DarcyJProjects/stm32-plc-project/Media/2.png

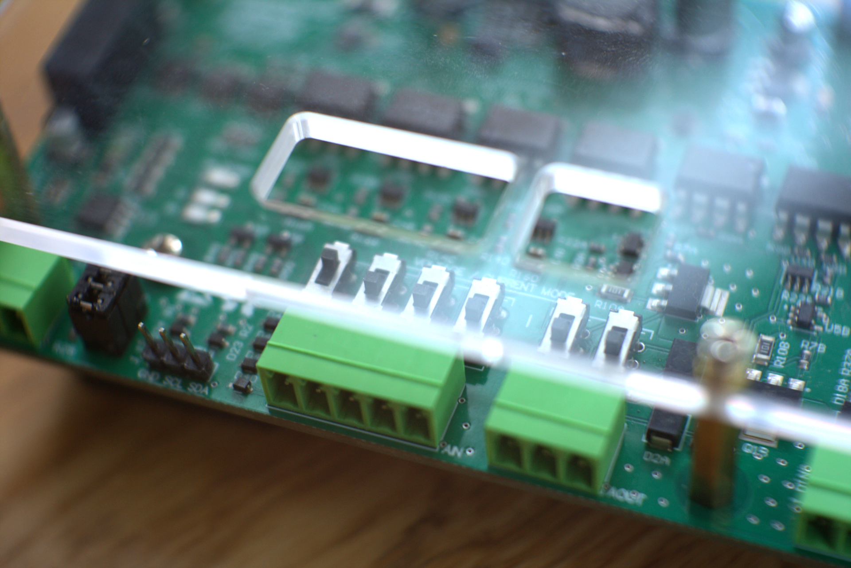
Media/2.png
