DarcyJProjects/stm32-plc-project/Media/4.png

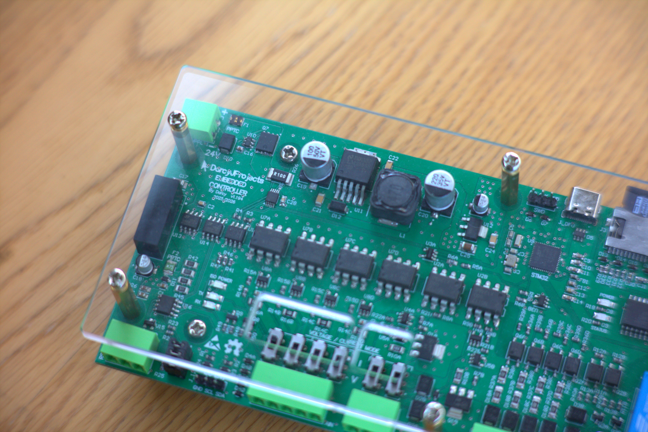
Media/4.png
