DarcyJProjects/stm32-plc-project/Firmware/Core/Src/modbus/modbus_vendor.c

#include <modbus/modbus_slave.h>
#include "modbus/modbus_vendor.h"
#include "modbus/modbus_util.h"
#include "automation/automation.h"
#include "io/io_virtual.h"
#include "rtc/rtc_ds3231.h"

#include "io/io_coils.h"
#include "io/io_holding_reg.h"
#include "io/io_emergency.h"

// Handle a full received modbus frame
void modbus_vendor_handle_frame(uint8_t* frame, uint16_t len) {
	uint8_t function = frame[1];
	uint8_t slave_address = modbusGetSlaveAddress();

	switch (function) {
		case MODBUS_VENDOR_FUNC_ADD_RULE: {
			// At least 4 bytes for overhead + 1 byte for rule_type
			if (len < 5) {
				modbus_send_exception(slave_address, function, MODBUS_EXCEPTION_ILLEGAL_DATA_VALUE);
				return;
			}

			uint8_t rule_type = frame[2];

			if (rule_type == 1) { // Logic Rule
				// Check if the frame length is correct: 19 + 4 (slave id (1), function (1), crc (2)) = 23
				if (len != 23) {
					modbus_send_exception(slave_address, function, MODBUS_EXCEPTION_ILLEGAL_DATA_VALUE);
					return;
				}

				// Extract fields from the payload (shifted by +1 due to rule_type)
				uint8_t input_type1Raw = frame[3];
				uint16_t input_reg1 = (frame[4] << 8) | frame[5];
				uint8_t op1Raw = frame[6];
				uint16_t compare_value1 = (frame[7] << 8) | frame[8];
				uint8_t input_type2Raw = frame[9];
				uint16_t input_reg2 = (frame[10] << 8) | frame[11];
				uint8_t op2Raw = frame[12];
				uint16_t compare_value2 = (frame[13] << 8) | frame[14];
				uint8_t joinRaw = frame[15];
				uint8_t output_typeRaw = frame[16];
				uint16_t output_reg = (frame[17] << 8) | frame[18];
				uint16_t output_value = (frame[19] << 8) | frame[20];

				// Validate fields
				if (input_type1Raw == 0 || input_type1Raw > AUTOMATION_TYPE_COUNT || output_typeRaw == 0 || output_typeRaw > AUTOMATION_TYPE_COUNT) {
					modbus_send_exception(slave_address, function, MODBUS_EXCEPTION_ILLEGAL_DATA_VALUE);
					return;
				}
				if ((joinRaw != 1) && (input_type2Raw == 0 || input_type2Raw > AUTOMATION_TYPE_COUNT)) {
					modbus_send_exception(slave_address, function, MODBUS_EXCEPTION_ILLEGAL_DATA_VALUE);
					return;
				}
				if (op1Raw == 0 || op1Raw > AUTOMATION_OPERATION_COUNT) {
					modbus_send_exception(slave_address, function, MODBUS_EXCEPTION_ILLEGAL_DATA_VALUE);
					return;
				}
				if ((joinRaw != 1) && (op2Raw == 0 || op2Raw > AUTOMATION_OPERATION_COUNT)) {
					modbus_send_exception(slave_address, function, MODBUS_EXCEPTION_ILLEGAL_DATA_VALUE);
					return;
				}
				if (joinRaw < 1 || joinRaw > AUTOMATION_JOIN_COUNT) {
					modbus_send_exception(slave_address, function, MODBUS_EXCEPTION_ILLEGAL_DATA_VALUE);
					return;
				}

				RegisterType input_type1 = input_type1Raw - 1;
				RegisterType output_type = output_typeRaw - 1;
				ComparisonOp op1 = op1Raw - 1;
				LogicJoin join = joinRaw - 1;

				RegisterType input_type2 = 0;
				ComparisonOp op2 = 0;
				if (joinRaw != 1) {
					input_type2 = input_type2Raw - 1;
					op2 = op2Raw - 1;
				}

				LogicRule newRule = {
					.input_type1 = input_type1,
					.input_reg1 = input_reg1,
					.op1 = op1,
					.compare_value1 = compare_value1,
					.input_type2 = input_type2,
					.input_reg2 = input_reg2,
					.op2 = op2,
					.compare_value2 = compare_value2,
					.join = join,
					.output_type = output_type,
					.output_reg = output_reg,
					.output_value = output_value
				};

				uint8_t statusByte = 0x01; // Successful
				if (!automation_add_rule(newRule)) {
					statusByte = 0x00; // Unsuccessful
				}

				// Create the response frame
				uint8_t responseData[3];
				responseData[0] = slave_address;
				responseData[1] = MODBUS_VENDOR_FUNC_ADD_RULE;
				responseData[2] = statusByte;
				modbus_send_response(responseData, 3);

			} else if (rule_type == 2) { // Copy Rule
				// Length: 7 payload + 4 overhead = 11
				if (len != 11) {
					modbus_send_exception(slave_address, function, MODBUS_EXCEPTION_ILLEGAL_DATA_VALUE);
					return;
				}

				uint8_t input_typeRaw = frame[3];
				uint16_t input_reg = (frame[4] << 8) | frame[5];
				uint8_t output_typeRaw = frame[6];
				uint16_t output_reg = (frame[7] << 8) | frame[8];

				// Validate types
				if (input_typeRaw == 0 || input_typeRaw > AUTOMATION_TYPE_COUNT || output_typeRaw == 0 || output_typeRaw > AUTOMATION_TYPE_COUNT) {
					modbus_send_exception(slave_address, function, MODBUS_EXCEPTION_ILLEGAL_DATA_VALUE);
					return;
				}

				CopyRule newRule = {
					.input_type = input_typeRaw - 1,
					.input_reg = input_reg,
					.output_type = output_typeRaw - 1,
					.output_reg = output_reg
				};

				uint8_t statusByte = 0x01;
				if (!automation_add_copyRule(newRule)) {
					statusByte = 0x00;
				}

				uint8_t responseData[3];
				responseData[0] = slave_address;
				responseData[1] = MODBUS_VENDOR_FUNC_ADD_RULE;
				responseData[2] = statusByte;
				modbus_send_response(responseData, 3);

			} else {
				modbus_send_exception(slave_address, function, MODBUS_EXCEPTION_ILLEGAL_DATA_VALUE);
			}
			break;
		}
		case MODBUS_VENDOR_FUNC_GET_RULE_COUNT: {
			// Check request length (Slave, Func, Type, Padding, CRC Low, CRC High) = 6
			if (len != 6) {
				modbus_send_exception(slave_address, function, MODBUS_EXCEPTION_ILLEGAL_DATA_VALUE);
				return;
			}

			uint8_t rule_type = frame[2];
			uint16_t count = 0;

			if (rule_type == 1) {
				count = automation_get_rule_count();
			} else if (rule_type == 2) {
				count = automation_get_copyRule_count();
			} else {
				modbus_send_exception(slave_address, function, MODBUS_EXCEPTION_ILLEGAL_DATA_VALUE);
				return;
			}

			// Create the response frame
			uint8_t responseData[5];

			responseData[0] = slave_address;
			responseData[1] = MODBUS_VENDOR_FUNC_GET_RULE_COUNT; // Fixed: originally was ADD_RULE
			responseData[2] = 0x02; // byte count, 2 bytes follow
			responseData[3] = count >> 8;
			responseData[4] = count & 0x00FF;

			modbus_send_response(responseData, 5);
			break;
		}
		case MODBUS_VENDOR_FUNC_GET_RULE: {
			// Check request length (Slave, Func, RuleType, Index High, Index Low, CRC Low, CRC High) = 7
			if (len != 7) {
				modbus_send_exception(slave_address, function, MODBUS_EXCEPTION_ILLEGAL_DATA_VALUE);
				return;
			}

			uint8_t rule_type = frame[2];
			uint16_t ruleIndex = (frame[3] << 8) | frame[4];
			uint8_t responseData[MODBUS_MAX_FRAME_SIZE];

			responseData[0] = slave_address;
			responseData[1] = MODBUS_VENDOR_FUNC_GET_RULE;

			if (rule_type == 1) { // Logic Rule
				LogicRule rule;
				if (!automation_get_rule(ruleIndex, &rule)) {
					modbus_send_exception(slave_address, function, MODBUS_EXCEPTION_SLAVE_DEVICE_FAILURE);
					return;
				}

				responseData[2] = (uint8_t)rule.input_type1 + 1;
				responseData[3] = (uint16_t)rule.input_reg1 >> 8;
				responseData[4] = (uint16_t)rule.input_reg1 & 0xFF;
				responseData[5] = (uint8_t)rule.op1 + 1;
				responseData[6] = (uint16_t)rule.compare_value1 >> 8;
				responseData[7] = (uint16_t)rule.compare_value1 & 0xFF;
				responseData[8] = (uint8_t)rule.input_type2 + 1;
				responseData[9] = (uint16_t)rule.input_reg2 >> 8;
				responseData[10] = (uint16_t)rule.input_reg2 & 0xFF;
				responseData[11] = (uint8_t)rule.op2 + 1;
				responseData[12] = (uint16_t)rule.compare_value2 >> 8;
				responseData[13] = (uint16_t)rule.compare_value2 & 0xFF;
				responseData[14] = (uint8_t)rule.join + 1;
				responseData[15] = (uint8_t)rule.output_type + 1;
				responseData[16] = (uint16_t)rule.output_reg >> 8;
				responseData[17] = (uint16_t)rule.output_reg & 0xFF;
				responseData[18] = (uint16_t)rule.output_value >> 8;
				responseData[19] = (uint16_t)rule.output_value & 0xFF;

				modbus_send_response(responseData, 20);

			} else if (rule_type == 2) { // Copy Rule
				CopyRule rule;
				if (!automation_get_copyRule(ruleIndex, &rule)) {
					modbus_send_exception(slave_address, function, MODBUS_EXCEPTION_SLAVE_DEVICE_FAILURE);
					return;
				}

				responseData[2] = (uint8_t)rule.input_type + 1;
				responseData[3] = (uint16_t)rule.input_reg >> 8;
				responseData[4] = (uint16_t)rule.input_reg & 0xFF;
				responseData[5] = (uint8_t)rule.output_type + 1;
				responseData[6] = (uint16_t)rule.output_reg >> 8;
				responseData[7] = (uint16_t)rule.output_reg & 0xFF;

				modbus_send_response(responseData, 8);
			} else {
				modbus_send_exception(slave_address, function, MODBUS_EXCEPTION_ILLEGAL_DATA_VALUE);
				return;
			}
			break;
		}
		case MODBUS_VENDOR_FUNC_DEL_RULE: {
			// Check request length (Slave, Func, RuleType, Index High, Index Low, CRC Low, CRC High) = 7
			if (len != 7) {
				modbus_send_exception(slave_address, function, MODBUS_EXCEPTION_ILLEGAL_DATA_VALUE);
				return;
			}

			uint8_t rule_type = frame[2];
			uint16_t ruleIndex = (frame[3] << 8) | frame[4];
			bool status = false;

			if (rule_type == 1) {
				status = automation_delete_rule(ruleIndex);
			} else if (rule_type == 2) {
				status = automation_delete_copyRule(ruleIndex);
			} else {
				modbus_send_exception(slave_address, function, MODBUS_EXCEPTION_ILLEGAL_DATA_VALUE);
				return;
			}

			if (status == false) {
				modbus_send_exception(slave_address, function, MODBUS_EXCEPTION_SLAVE_DEVICE_FAILURE);
				return;
			}

			// Create the response frame
			uint8_t responseData[3];
			responseData[0] = slave_address;
			responseData[1] = MODBUS_VENDOR_FUNC_DEL_RULE;
			responseData[2] = 0x01; // Success

			modbus_send_response(responseData, 3);
			break;
		}
		case MODBUS_VENDOR_FUNC_ADD_VIRTUAL_REG: {
			// Check request length (Slave Address, Function Code, Register Type, 0x00, CRC Low, CRC High)
			if (len != 6) {
				modbus_send_exception(slave_address, function, MODBUS_EXCEPTION_ILLEGAL_DATA_VALUE);
				return;
			}

			if (frame[2] == 0 || frame[2] > 2) {
				modbus_send_exception(slave_address, function, MODBUS_EXCEPTION_ILLEGAL_DATA_VALUE);
				return;
			}

			VirtualRegisterType registerType = frame[2] - 1; // register type should start at 1 when sent over modbus

			bool status = io_virtual_add(registerType);
			if (status == false) {
				modbus_send_exception(slave_address, function, MODBUS_EXCEPTION_SLAVE_DEVICE_FAILURE);
				return;
			}

			// Create the response frame
			uint8_t responseData[3];

			responseData[0] = slave_address; // the address of us
			responseData[1] = MODBUS_VENDOR_FUNC_ADD_VIRTUAL_REG;
			responseData[2] = 0x01; // status

			uint16_t responseLen = 3;

			modbus_send_response(responseData, responseLen);
			break;
		}
		case MODBUS_VENDOR_FUNC_READ_VIRTUAL_REG: {
			// Check request length (Slave Address, Function Code, Register Type, Address High, Address Low, CRC Low, CRC High)
			if (len != 7) {
				modbus_send_exception(slave_address, function, MODBUS_EXCEPTION_ILLEGAL_DATA_VALUE);
				return;
			}

			// Verify type
			if (frame[2] == 0 || frame[2] > 2) {
				modbus_send_exception(slave_address, function, MODBUS_EXCEPTION_ILLEGAL_DATA_VALUE);
				return;
			}

			VirtualRegisterType registerType = frame[2] - 1; // register type should start at 1 when sent over modbus

			// Get Address
			uint16_t address = frame[3] << 8 | frame[4];

			uint16_t value;
			bool status = io_virtual_read(registerType, address, &value);
			if (status == false) {
				modbus_send_exception(slave_address, function, MODBUS_EXCEPTION_SLAVE_DEVICE_FAILURE);
				return;
			}


			// Create the response frame
			uint8_t byteCount;
			switch (registerType) {
				case VIR_COIL:
					byteCount = 1;
					break;
				case VIR_HOLDING:
					byteCount = 2;
					break;
			}

			uint8_t responseData[MODBUS_MAX_FRAME_SIZE];

			responseData[0] = slave_address; // the address of us
			responseData[1] = MODBUS_VENDOR_FUNC_READ_VIRTUAL_REG;
			responseData[2] = byteCount;

			switch (registerType) {
				case VIR_COIL:
					responseData[3] = (value != 0) ? 1 : 0;
					break;
				case VIR_HOLDING:
					responseData[3] = value >> 8; // high byte
					responseData[4] = value & 0xFF; // low byte
					break;
			}

			uint16_t responseLen = 3 + byteCount; // slave address, function, byte count, (byte count bytes)

			modbus_send_response(responseData, responseLen);
			break;
		}
		case MODBUS_VENDOR_FUNC_WRITE_VIRTUAL_REG: {
			// Check request length (Slave Address, Function Code, Register Type, Address High, Address Low, Value High, Value Low, CRC Low, CRC High)
			if (len != 9) {
				modbus_send_exception(slave_address, function, MODBUS_EXCEPTION_ILLEGAL_DATA_VALUE);
				return;
			}

			// Verify type
			if (frame[2] == 0 || frame[2] > 2) {
				modbus_send_exception(slave_address, function, MODBUS_EXCEPTION_ILLEGAL_DATA_VALUE);
				return;
			}

			VirtualRegisterType registerType = frame[2] - 1; // register type should start at 1 when sent over modbus

			// Get Address and value
			uint16_t address = (frame[3] << 8) | frame[4];
			uint16_t value = (frame[5] << 8) | frame[6];


			bool status = io_virtual_write(registerType, address, value);
			if (status == false) {
				modbus_send_exception(slave_address, function, MODBUS_EXCEPTION_SLAVE_DEVICE_FAILURE);
				return;
			}

			// Create the response frame
			uint16_t responseLen = 3; // slave address, function, status byte
			uint8_t responseData[MODBUS_MAX_FRAME_SIZE];

			responseData[0] = slave_address; // the address of us
			responseData[1] = MODBUS_VENDOR_FUNC_WRITE_VIRTUAL_REG;
			responseData[2] = 0x01; // 0x01 = success

			modbus_send_response(responseData, responseLen);
			break;
		}
		case MODBUS_VENDOR_FUNC_GET_VIRTUAL_REG_COUNT: {
			// Check request length (Slave Address, Function Code, Register Type, 0x00, CRC Low, CRC High)
			if (len != 6) {
				modbus_send_exception(slave_address, function, MODBUS_EXCEPTION_ILLEGAL_DATA_VALUE);
				return;
			}

			// Verify type
			if (frame[2] == 0 || frame[2] > 2) {
				modbus_send_exception(slave_address, function, MODBUS_EXCEPTION_ILLEGAL_DATA_VALUE);
				return;
			}

			VirtualRegisterType registerType = frame[2] - 1; // register type should start at 1 when sent over modbus

			uint16_t count;
			bool status = io_virtual_get_count(registerType, &count);
			if (status == false) {
				modbus_send_exception(slave_address, function, MODBUS_EXCEPTION_SLAVE_DEVICE_FAILURE);
				return;
			}

			// Create the response frame
			uint8_t responseData[MODBUS_MAX_FRAME_SIZE];

			responseData[0] = slave_address; // the address of us
			responseData[1] = MODBUS_VENDOR_FUNC_GET_VIRTUAL_REG_COUNT;
			responseData[2] = 0x02; // byte count
			responseData[3] = count >> 8; // high byte
			responseData[4] = count & 0xFF; // low byte

			uint16_t responseLen = 5;

			modbus_send_response(responseData, responseLen);
			break;
		}
		case MODBUS_VENDOR_FUNC_CLEAR_VIRTUAL_REG: {
			// Check request length (Slave Address, Function Code, 0x01, 0x01, CRC Low, CRC High)
			// must send two 0x01 bytes to confirm
			if (len != 6) {
				modbus_send_exception(slave_address, function, MODBUS_EXCEPTION_ILLEGAL_DATA_VALUE);
				return;
			}

			if (frame[2] != 1 || frame[3] != 1) {
				modbus_send_exception(slave_address, function, MODBUS_EXCEPTION_ILLEGAL_DATA_VALUE);
				return;
			}


			bool status = io_virtual_clear();
			if (status == false) {
				modbus_send_exception(slave_address, function, MODBUS_EXCEPTION_SLAVE_DEVICE_FAILURE);
				return;
			}

			// Create the response frame
			uint8_t responseData[3];

			responseData[0] = slave_address; // the address of us
			responseData[1] = MODBUS_VENDOR_FUNC_CLEAR_VIRTUAL_REG;
			responseData[2] = 0x01; // status

			uint16_t responseLen = 3;

			modbus_send_response(responseData, responseLen);
			break;
		}
		case MODBUS_VENDOR_FUNC_SET_RTC: {
			// Check request length (Slave Address, Function Code, 7x data, CRC Low, CRC High)
			if (len != 11) {
				modbus_send_exception(slave_address, function, MODBUS_EXCEPTION_ILLEGAL_DATA_VALUE);
				return;
			}

			RTC_Time setTime;
			setTime.seconds 	= frame[2];
			setTime.minutes		= frame[3];
			setTime.hours		= frame[4];
			setTime.day_of_week	= frame[5];
			setTime.day			= frame[6];
			setTime.month		= frame[7];
			setTime.year		= frame[8];

			// Set time on DS3231
			HAL_StatusTypeDef status = DS3231_SetTime(&setTime);
			if (status != HAL_OK) {
				modbus_send_exception(slave_address, function, MODBUS_EXCEPTION_SLAVE_DEVICE_FAILURE);
				return;
			}

			// Create the response frame
			uint8_t responseData[MODBUS_MAX_FRAME_SIZE];

			responseData[0] = slave_address; // the address of us
			responseData[1] = MODBUS_VENDOR_FUNC_SET_RTC;
			responseData[2] = 0x01; // status byte (0x01 = success)

			uint16_t responseLen = 3;

			modbus_send_response(responseData, responseLen);
			break;
		}
		case MODBUS_VENDOR_FUNC_SET_HOLDING_REG_MODE: {
			uint16_t index = (frame[2] << 8) | frame[3];
			IO_Holding_Reg_Mode mode = frame[4] - 1;

			// Check request length (Slave Address, Function Code, Index High, Index Low, Mode [1 = voltage, 2 = current], CRC Low, CRC High)
			if (len != 7) {
				modbus_send_exception(slave_address, function, MODBUS_EXCEPTION_ILLEGAL_DATA_VALUE);
				return;
			}

			// Check mode
			if (frame[4] < 1 || frame[4] > 2) {
			    modbus_send_exception(slave_address, function, MODBUS_EXCEPTION_ILLEGAL_DATA_VALUE);
			    return;
			}

			// Set the mode of the holding register
			if (!io_holding_reg_set_mode(index, mode)) {
				modbus_send_exception(slave_address, function, MODBUS_EXCEPTION_SLAVE_DEVICE_FAILURE);
				return;
			}

			// Create the response frame
			uint8_t responseData[MODBUS_MAX_FRAME_SIZE];

			responseData[0] = slave_address; // the address of us
			responseData[1] = MODBUS_VENDOR_FUNC_SET_HOLDING_REG_MODE;
			responseData[2] = 0x01; // status byte (0x01 = success)

			uint16_t responseLen = 3;

			modbus_send_response(responseData, responseLen);
			break;
		}
		case MODBUS_VENDOR_FUNC_SET_INPUT_REG_MODE: {
			uint16_t index = (frame[2] << 8) | frame[3];
			IO_Input_Reg_Mode mode = frame[4] - 1;

			// Check request length (Slave Address, Function Code, Index High, Index Low, Mode [1 = voltage, 2 = current], CRC Low, CRC High)
			if (len != 7) {
				modbus_send_exception(slave_address, function, MODBUS_EXCEPTION_ILLEGAL_DATA_VALUE);
				return;
			}

			// Check mode
			if (frame[4] < 1 || frame[4] > 2) {
				modbus_send_exception(slave_address, function, MODBUS_EXCEPTION_ILLEGAL_DATA_VALUE);
				return;
			}

			// Set the mode of the input register
			if (!io_input_reg_set_mode(index, mode)) {
				modbus_send_exception(slave_address, function, MODBUS_EXCEPTION_SLAVE_DEVICE_FAILURE);
				return;
			}

			// Create the response frame
			uint8_t responseData[MODBUS_MAX_FRAME_SIZE];

			responseData[0] = slave_address; // the address of us
			responseData[1] = MODBUS_VENDOR_FUNC_SET_INPUT_REG_MODE;
			responseData[2] = 0x01; // status byte (0x01 = success)

			uint16_t responseLen = 3;

			modbus_send_response(responseData, responseLen);
			break;
		}
		case MODBUS_VENDOR_FUNC_GET_REG_MODE: {
			uint16_t index = (frame[2] << 8) | frame[3];
			uint8_t type = frame[4]; // 3 = holding, 4 = input (1, 2 for coil & discrete are irrelevant)

			// Check request length (Slave Address, Function Code, Index High, Index Low, type integer, CRC Low, CRC High)
			if (len != 7) {
				modbus_send_exception(slave_address, function, MODBUS_EXCEPTION_ILLEGAL_DATA_VALUE);
				return;
			}

			// Get the mode of the holding register
			uint8_t mode;
			if (type == 3) {
				IO_Holding_Reg_Mode regMode;
				if (!io_holding_reg_get_mode(index, &regMode)) {
					modbus_send_exception(slave_address, function, MODBUS_EXCEPTION_SLAVE_DEVICE_FAILURE);
					return;
				}
				mode = (uint8_t)(regMode);
			} else if (type == 4) {
				IO_Input_Reg_Mode regMode;
				if (!io_input_reg_get_mode(index, &regMode)) {
					modbus_send_exception(slave_address, function, MODBUS_EXCEPTION_SLAVE_DEVICE_FAILURE);
					return;
				}
				mode = (uint8_t)(regMode);
			}

			// Create the response frame
			uint8_t responseData[MODBUS_MAX_FRAME_SIZE];

			responseData[0] = slave_address; // the address of us
			responseData[1] = MODBUS_VENDOR_FUNC_GET_REG_MODE;
			responseData[2] = mode + 1; // mode

			uint16_t responseLen = 3;

			modbus_send_response(responseData, responseLen);
			break;
		}
		case MODBUS_VENDOR_FUNC_SET_EMERGENCY_STOP: {
			uint16_t channel = (frame[2] << 8) | frame[3];
			Emergency_Stop_Input_Mode inputMode = frame[4] - 1;

			// Check request length (Slave Address, Function Code, Index High, Index Low, Input Mode [1 = NO, 2 = NC], CRC Low, CRC High)
			if (len != 7) {
				modbus_send_exception(slave_address, function, MODBUS_EXCEPTION_ILLEGAL_DATA_VALUE);
				return;
			}

			// Check inputMode
			if (frame[4] < 1 || frame[4] > 2) {
				modbus_send_exception(slave_address, function, MODBUS_EXCEPTION_ILLEGAL_DATA_VALUE);
				return;
			}

			// Set the emergency stop configuration
			if (!emergencyStop_setInput(channel, inputMode)) {
				modbus_send_exception(slave_address, function, MODBUS_EXCEPTION_SLAVE_DEVICE_FAILURE);
				return;
			}

			// Create the response frame
			uint8_t responseData[MODBUS_MAX_FRAME_SIZE];

			responseData[0] = slave_address; // the address of us
			responseData[1] = MODBUS_VENDOR_FUNC_SET_EMERGENCY_STOP;
			responseData[2] = 0x01; // status byte (0x01 = success)

			uint16_t responseLen = 3;

			modbus_send_response(responseData, responseLen);
			break;
		}
		case MODBUS_VENDOR_FUNC_FACTORY_RESET: {
			uint8_t confirmation = frame[2];

			// Check request length (Slave Address, Function Code, Confirmation, Padding, CRC Low, CRC High)
			if (len != 6) {
				modbus_send_exception(slave_address, function, MODBUS_EXCEPTION_ILLEGAL_DATA_VALUE);
				return;
			}

			// Check confirmation
			if (confirmation != 1) {
				modbus_send_exception(slave_address, function, MODBUS_EXCEPTION_ILLEGAL_DATA_VALUE);
				return;
			}

			// Factory Reset
			if (!automation_factory_reset()) {
				modbus_send_exception(slave_address, function, MODBUS_EXCEPTION_SLAVE_DEVICE_FAILURE);
				return;
			}

			// Create the response frame
			uint8_t responseData[MODBUS_MAX_FRAME_SIZE];

			responseData[0] = slave_address; // the address of us
			responseData[1] = MODBUS_VENDOR_FUNC_FACTORY_RESET;
			responseData[2] = 0x01; // status byte (0x01 = success)

			uint16_t responseLen = 3;

			modbus_send_response(responseData, responseLen);
			break;
		}
		default: {
			modbus_send_exception(slave_address, function, MODBUS_EXCEPTION_ILLEGAL_FUNCTION);
			break;
		}
	}
}
