DarcyJProjects/stm32-plc-project/Firmware/Core/Src/i2c/display.c

#include <i2c/ina226.h>
#include <modbus/modbus_slave.h>
#include "i2c/display.h"
#include "i2c/ssd1306/ssd1306.h"
#include "i2c/ssd1306/ssd1306_fonts.h"
#include "i2c/ssd1306/ssd1306_icons.h"
#include "io/io_coils.h"
#include "rtc/rtc_ds3231.h"
#include "io/io_virtual.h"
#include "sd/sd.h"

#include "i2c/icons.h"
extern const unsigned char icon_sd_16x17 [];

#include <stdlib.h> // for rand()
#include <time.h> // for seeding rand


// Variables
static uint16_t currentPage = 0;
static uint16_t endPage = 10;

// Burn in prevention
static int8_t offsetX = 0;
static int8_t offsetY = 0;
static uint32_t lastShiftTime = 0;
const uint32_t shiftIntervalMs = 30000; // Cannot be less than how often display_StatusPage is called. 60000: every minute

// Heartbeat
static bool doHearthbeat = false;
static uint8_t heartbeatOn = 0;
static uint32_t lastHeartbeatTime = 0;
const uint32_t heartbeatIntervalMs = 1000; // 1s - Cannot be less than how often display_StatusPage is called.

// Uptime
RTC_Time startTime = {0};

void display_Setup() {
	// Initialise SSD1306
	ssd1306_Init();

	// Entropy source
	srand(HAL_GetTick()); // seed the random number generator

	// Get start time
	DS3231_ReadTime(&startTime);
}

void display_Boot(void) {
	ssd1306_Fill(Black);
	ssd1306_SetCursor(10, 10);
	ssd1306_WriteString("PLC by DJ", Font_11x18, White);
	ssd1306_SetCursor(25, 35);
	ssd1306_WriteString("Booting...", Font_7x10, White);
	ssd1306_UpdateScreen();
}

static void display_SetCursor(uint8_t x, uint8_t y) {
	ssd1306_SetCursor(x + offsetX, y + offsetY);
}

static int8_t display_RandOffset(void) {
	return (rand() % 3) - 1; // random number from -1 to 1
}


static uint32_t rtcToSeconds(RTC_Time t) {
    uint32_t days = 0;

    // Days per month for non-leap year
    const uint8_t daysInMonth[] = {31,28,31,30,31,30,31,31,30,31,30,31};

    // Check leap year helper
    bool isLeapYear(uint8_t year) {
        uint16_t fullYear = 2000 + year;
        return (fullYear % 4 == 0 && (fullYear % 100 != 0 || fullYear % 400 == 0));
    }

    // Add days for full years passed
    for (uint8_t y = 0; y < t.year; y++) {
        days += isLeapYear(y) ? 366 : 365;
    }

    // Add days for full months passed this year
    for (uint8_t m = 1; m < t.month; m++) {
        days += daysInMonth[m - 1];
        if (m == 2 && isLeapYear(t.year)) days += 1; // leap day
    }

    // Add days passed this month
    days += t.day - 1;

    // Calculate total seconds
    return (((days * 24UL + t.hours) * 60 + t.minutes) * 60 + t.seconds);
}



void display_StatusPage(void) {
	uint32_t now = HAL_GetTick();

	if ((uint32_t)(now - lastShiftTime) > shiftIntervalMs) {
		offsetX = display_RandOffset();
		offsetY = abs(display_RandOffset());
		lastShiftTime = now;
	}

	char buf[32]; // buffer for formatted strings

	ssd1306_Fill(Black);

	// heartbeat
	if (doHearthbeat) {
		if ((uint32_t)(now - lastHeartbeatTime) > heartbeatIntervalMs) {
			heartbeatOn = !heartbeatOn;
			lastHeartbeatTime = now;
		}

		if (currentPage == 0) {
			if (heartbeatOn) {
				ssd1306_FillCircle(120 + offsetX, 8 + offsetY, 4, White); // filled 4px circle
			} else {
				ssd1306_DrawCircle(120 + offsetX, 8 + offsetY, 4, White); // hollow 4px circle
			}

		}
	}

	switch(currentPage) {
		case 0:
			display_SetCursor(25, 0);
			ssd1306_WriteString("Status", Font_11x18, White);

			display_SetCursor(2, 25);
			sprintf(buf, "Slave Addr: 0x%02X", modbusGetSlaveAddress());
			ssd1306_WriteString(buf, Font_6x8, White);

			display_SetCursor(2, 40);
			float voltage = INA226_ReadBusVoltage();
			if (voltage > 10) sprintf(buf, "Supply: %.1fV", voltage); // only 1dp will fit
			else sprintf(buf, "Supply: %.2fV", voltage); // 2dp will fit
			ssd1306_WriteString(buf, Font_6x8, White);

			display_SetCursor(2, 55);
			sprintf(buf, "Current: %.0fmA", INA226_ReadCurrent() * 1000);
			ssd1306_WriteString(buf, Font_6x8, White);
			break;
		case 1:
			display_SetCursor(30, 0);
			ssd1306_WriteString("Coils", Font_11x18, White);

			display_SetCursor(2, 25);
			sprintf(buf, "0: %s", io_coil_read(0) ? "ON" : "OFF");
			ssd1306_WriteString(buf, Font_6x8, White);

			display_SetCursor(2, 40);
			sprintf(buf, "1: %s", io_coil_read(1) ? "ON" : "OFF");
			ssd1306_WriteString(buf, Font_6x8, White);

			display_SetCursor(60, 25);
			sprintf(buf, "2: %s", io_coil_read(2) ? "ON" : "OFF");
			ssd1306_WriteString(buf, Font_6x8, White);

			display_SetCursor(60, 40);
			sprintf(buf, "3: %s", io_coil_read(3) ? "ON" : "OFF");
			ssd1306_WriteString(buf, Font_6x8, White);
			break;
		case 2:
			display_SetCursor(4, 0);
			ssd1306_WriteString("Discrete In", Font_11x18, White);

			display_SetCursor(2, 25);
			sprintf(buf, "0: %s", io_discrete_in_read(0) ? "ON" : "OFF");
			ssd1306_WriteString(buf, Font_6x8, White);

			display_SetCursor(2, 40);
			sprintf(buf, "1: %s", io_discrete_in_read(1) ? "ON" : "OFF");
			ssd1306_WriteString(buf, Font_6x8, White);

			display_SetCursor(60, 25);
			sprintf(buf, "2: %s", io_discrete_in_read(2) ? "ON" : "OFF");
			ssd1306_WriteString(buf, Font_6x8, White);

			display_SetCursor(60, 40);
			sprintf(buf, "3: %s", io_discrete_in_read(3) ? "ON" : "OFF");
			ssd1306_WriteString(buf, Font_6x8, White);
			break;
		case 3:
			display_SetCursor(2, 0);
			ssd1306_WriteString("Holding Reg", Font_11x18, White);

			display_SetCursor(2, 25);
			sprintf(buf, "0: %d", io_holding_reg_read(0));
			ssd1306_WriteString(buf, Font_6x8, White);

			display_SetCursor(2, 40);
			sprintf(buf, "1: %d", io_holding_reg_read(1));
			ssd1306_WriteString(buf, Font_6x8, White);

			/*display_SetCursor(60, 25);
			sprintf(buf, "2: %d", io_holding_reg_read(2));
			ssd1306_WriteString(buf, Font_6x8, White);

			display_SetCursor(60, 40);
			sprintf(buf, "3: %d", io_holding_reg_read(3));
			ssd1306_WriteString(buf, Font_6x8, White);*/
			break;
		case 4:
			display_SetCursor(2, 0);
			ssd1306_WriteString("Holding Reg", Font_11x18, White);

			display_SetCursor(2, 25);
			IO_Holding_Reg_Mode mode0hr;
			io_holding_reg_get_mode(0, &mode0hr);
			sprintf(buf, "0: %s", mode0hr == IO_HOLDING_REG_VOLTAGE ? "0-5V" : "4-20mA");
			ssd1306_WriteString(buf, Font_6x8, White);

			display_SetCursor(2, 40);
			IO_Holding_Reg_Mode mode1hr;
			io_holding_reg_get_mode(1, &mode1hr);
			sprintf(buf, "1: %s", mode1hr == IO_HOLDING_REG_VOLTAGE ? "0-5V" : "4-20mA");
			ssd1306_WriteString(buf, Font_6x8, White);

			break;
		case 5:
			display_SetCursor(12, 0);
			ssd1306_WriteString("Input Reg", Font_11x18, White);

			display_SetCursor(2, 25);
			sprintf(buf, "0: %d", io_input_reg_read(0));
			ssd1306_WriteString(buf, Font_6x8, White);

			display_SetCursor(2, 40);
			sprintf(buf, "1: %d", io_input_reg_read(1));
			ssd1306_WriteString(buf, Font_6x8, White);

			display_SetCursor(60, 25);
			sprintf(buf, "2: %d", io_input_reg_read(2));
			ssd1306_WriteString(buf, Font_6x8, White);

			display_SetCursor(60, 40);
			sprintf(buf, "3: %d", io_input_reg_read(3));
			ssd1306_WriteString(buf, Font_6x8, White);
			break;
		case 6:
			display_SetCursor(12, 0);
			ssd1306_WriteString("Input Reg", Font_11x18, White);

			display_SetCursor(2, 25);
			IO_Input_Reg_Mode mode0ir;
			io_input_reg_get_mode(0, &mode0ir);
			sprintf(buf, "0: %s", mode0ir == IO_INPUT_REG_VOLTAGE ? "0-5V" : "4-20mA");
			ssd1306_WriteString(buf, Font_6x8, White);

			display_SetCursor(2, 40);
			IO_Input_Reg_Mode mode1ir;
			io_input_reg_get_mode(1, &mode1ir);
			sprintf(buf, "1: %s", mode1ir == IO_INPUT_REG_VOLTAGE ? "0-5V" : "4-20mA");
			ssd1306_WriteString(buf, Font_6x8, White);

			display_SetCursor(60, 25);
			IO_Input_Reg_Mode mode2ir;
			io_input_reg_get_mode(2, &mode2ir);
			sprintf(buf, "2: %s", mode2ir == IO_INPUT_REG_VOLTAGE ? "0-5V" : "4-20mA");
			ssd1306_WriteString(buf, Font_6x8, White);

			display_SetCursor(60, 40);
			IO_Input_Reg_Mode mode3ir;
			io_input_reg_get_mode(3, &mode3ir);
			sprintf(buf, "3: %s", mode3ir == IO_INPUT_REG_VOLTAGE ? "0-5V" : "4-20mA");
			ssd1306_WriteString(buf, Font_6x8, White);

			break;
		case 7:
			display_SetCursor(7, 0);
			ssd1306_WriteString("Automation", Font_11x18, White);

			display_SetCursor(2, 25);
			sprintf(buf, "%d rules", automation_get_rule_count());
			ssd1306_WriteString(buf, Font_6x8, White);

			uint16_t virtCoils = 0;
			uint16_t virtHolding = 0;
			io_virtual_get_count(VIR_COIL, &virtCoils);
			io_virtual_get_count(VIR_HOLDING, &virtHolding);

			display_SetCursor(2, 40);
			sprintf(buf, "%d virt. coils", virtCoils);
			ssd1306_WriteString(buf, Font_6x8, White);

			display_SetCursor(2, 55);
			sprintf(buf, "%d virt. holding", virtHolding);
			ssd1306_WriteString(buf, Font_6x8, White);
			break;
		case 8:
			display_SetCursor(50, 0);
			ssd1306_WriteString("RTC", Font_11x18, White);

			RTC_Time current;
			DS3231_ReadTime(&current);

			uint32_t nowSecs = rtcToSeconds(current);
			uint32_t bootSecs = rtcToSeconds(startTime);
			uint32_t uptimeSecs = nowSecs - bootSecs;

			uint32_t days    = uptimeSecs / 86400;
			uint32_t hours   = (uptimeSecs % 86400) / 3600;
			uint32_t minutes = (uptimeSecs % 3600) / 60;
			uint32_t seconds = uptimeSecs % 60;

			display_SetCursor(2, 25);
			if (days > 0) {
				sprintf(buf, "Uptime: %lud %02lu:%02lu:%02lu", days, hours, minutes, seconds);
			} else {
				sprintf(buf, "Uptime: %02lu:%02lu:%02lu", hours, minutes, seconds);
			}
			ssd1306_WriteString(buf, Font_6x8, White);

			display_SetCursor(2, 40);
			sprintf(buf, "Date: %02d/%02d/20%02d", current.day, current.month, current.year);
			ssd1306_WriteString(buf, Font_6x8, White);

			display_SetCursor(2, 55);
			sprintf(buf, "Time: %02d:%02d:%02d", current.hours, current.minutes, current.seconds);
			ssd1306_WriteString(buf, Font_6x8, White);
			break;
		case 9:
			display_SetCursor(5, 0);
			ssd1306_WriteString("Emerg. Stop", Font_11x18, White);

			bool defined = emergencyStop_isDefined();

			display_SetCursor(2, 25);
			sprintf(buf, "Enabled: %s", defined ? "true" : "false");
			ssd1306_WriteString(buf, Font_6x8, White);

			display_SetCursor(2, 40);
			if (defined) {
			    sprintf(buf, "D. Input: %u", emergencyStop_getChannel());
			} else {
			    sprintf(buf, "D. Input: -");
			}
			ssd1306_WriteString(buf, Font_6x8, White);

			display_SetCursor(2, 55);
			sprintf(buf, "Input Mode: %s", defined ? (emergencyStop_getInputMode() == EMERGENCY_STOP_NO ? "NO" : "NC") : "-");
			ssd1306_WriteString(buf, Font_6x8, White);
			break;
		case 10:
			display_SetCursor(5, 0);
			ssd1306_WriteString("SD Logging", Font_11x18, White);

			bool isMounted = SD_IsMounted();

			SD_Stats stats = SD_GetStats();

			display_SetCursor(2, 25);
			sprintf(buf, "Mounted: %s", isMounted ? "true" : "false");
			ssd1306_WriteString(buf, Font_6x8, White);

			display_SetCursor(2, 40);
			if (stats.success) {
				sprintf(buf, "Size: %luMB", stats.totalMB);
			} else {
				sprintf(buf, "Size: -");
			}
			ssd1306_WriteString(buf, Font_6x8, White);

			display_SetCursor(2, 55);
			if (stats.success) {
				sprintf(buf, "Free: %luMB", stats.freeMB);
			} else {
				sprintf(buf, "Free: -");
			}
			ssd1306_WriteString(buf, Font_6x8, White);
			break;
	}


	if (currentPage >= 10) {
		display_SetCursor(95, 55);
	} else {
		display_SetCursor(100, 55);
	}
	sprintf(buf, "%d/%d", currentPage, endPage);
	ssd1306_WriteString(buf, Font_6x8, White);

	ssd1306_UpdateScreen();
}

void display_FactoryResetPage(uint8_t page) {
	ssd1306_Fill(Black);
	ssd1306_SetCursor(25, 0);
	ssd1306_WriteString("RESET", Font_11x18, White);

	switch (page) {
		case 0:
			ssd1306_SetCursor(2, 25);
			ssd1306_WriteString("Continue holding", Font_6x8, White);

			ssd1306_SetCursor(2, 40);
			ssd1306_WriteString("for 5 seconds.", Font_6x8, White);
			break;
		case 1:
			ssd1306_SetCursor(2, 25);
			ssd1306_WriteString("Reset successful.", Font_6x8, White);

			ssd1306_SetCursor(2, 40);
			ssd1306_WriteString("Booting...", Font_6x8, White);
			break;
		case 2:
			ssd1306_SetCursor(2, 25);
			ssd1306_WriteString("Reset unsuccessful!", Font_6x8, White);

			ssd1306_SetCursor(2, 40);
			ssd1306_WriteString("Booting...", Font_6x8, White);
			break;
		case 3:
			ssd1306_SetCursor(2, 25);
			ssd1306_WriteString("Reset cancelled.", Font_6x8, White);

			ssd1306_SetCursor(2, 40);
			ssd1306_WriteString("Booting...", Font_6x8, White);
			break;
	}

	ssd1306_UpdateScreen();
}

void display_EmergencyStop(void) {
	ssd1306_Fill(Black);
	ssd1306_SetCursor(5, 0);
	ssd1306_WriteString("EMERGENCY", Font_11x18, White);

	ssd1306_SetCursor(2, 25);
	ssd1306_WriteString("All outputs set OFF.", Font_6x8, White);

	ssd1306_SetCursor(2, 40);
	ssd1306_WriteString("Reboot to reset.", Font_6x8, White);

	ssd1306_UpdateScreen();
}

void display_dfu(void) {
	ssd1306_Fill(Black);
	ssd1306_SetCursor(15, 10);
	ssd1306_WriteString("DFU Mode", Font_11x18, White);

	ssd1306_SetCursor(10, 35);
	ssd1306_WriteString("Ready for upload", Font_6x8, White);

	ssd1306_SetCursor(30, 45);
	ssd1306_WriteString("over usb.", Font_6x8, White);

	ssd1306_UpdateScreen();
}

void display_BtnPress() {
	if (currentPage == endPage) {
		currentPage = 0;
	}
	else {
		currentPage++;
	}

	display_StatusPage();
}

void display_setPage(uint16_t page) {
	if (page > endPage) return;
	currentPage = page;
}

void display_sd_status(SD_Status sd_status)
{
	ssd1306_Fill(Black);

	ssd1306_DrawBitmap(15, 2, icon_sd_16x17, 16, 17, White);

	ssd1306_SetCursor(38, 2);
	ssd1306_WriteString("SD Card", Font_11x18, White);

	switch (sd_status) {
		case SD_INSERTED_MOUNT_FAILURE:
			ssd1306_SetCursor(16, 28);
			ssd1306_WriteString("SD Card Inserted", Font_6x8, White);

			ssd1306_SetCursor(16, 40);
			ssd1306_WriteString("Mounting failed!", Font_6x8, White);
			break;
		case SD_INSERTED_MOUNT_SUCCESS:
			ssd1306_SetCursor(16, 28);
			ssd1306_WriteString("SD Card Inserted", Font_6x8, White);

			ssd1306_SetCursor(10, 40);
			ssd1306_WriteString("Mounting succeeded", Font_6x8, White);
			break;
		case SD_REMOVED:
			ssd1306_SetCursor(16, 28);
			ssd1306_WriteString("SD Card Removed!", Font_6x8, White);

			ssd1306_SetCursor(22, 40);
			ssd1306_WriteString("Forced unmount", Font_6x8, White);
			break;
		default:
			return;
	}

	ssd1306_UpdateScreen();
}
