DarcyJProjects/stm32-plc-project/Firmware/Core/Src/i2c/icons.c

#include "i2c/icons.h"

// 'sd', 16x17px
const unsigned char icon_sd_16x17 [] = {
		0x1f, 0xf8, 0x20, 0x08, 0x2a, 0xa8, 0x4a, 0xa8, 0x8a, 0xa8, 0x80, 0x08, 0xc0, 0x08, 0x40, 0x08,
		0xcd, 0x88, 0x91, 0x48, 0x89, 0x48, 0x85, 0x48, 0x99, 0x88, 0x80, 0x08, 0x80, 0x08, 0x80, 0x08,
		0xff, 0xf8
	};
