DarcyJProjects/stm32-plc-project/Firmware/Core/Src/splash_screens/screen0.c

#include "splash_screens/screen0.h"

// 'cursor_12_19', 12x19px
const unsigned char sprite_cursor_12_19 [] = {
	0x80, 0x00, 0xc0, 0x00, 0xe0, 0x00, 0xf0, 0x00, 0xf8, 0x00, 0xfc, 0x00, 0xfe, 0x00, 0xff, 0x00,
	0xff, 0x80, 0xff, 0xc0, 0xff, 0xe0, 0xff, 0xf0, 0xfe, 0x00, 0xee, 0x00, 0xc6, 0x00, 0xc3, 0x00,
	0x83, 0x00, 0x01, 0x80, 0x01, 0x80
};

const AnimationStep screen0_path [] = {
    {113, 60}, {108, 54}, {101, 47}, {93, 42},
    {84, 38},  {76, 33},  {65, 31},  {53, 28},
    {43, 26},  {30, 24},  {21, 23},  {16, 23},
    {12, 23},  {8, 23}
};

const uint16_t screen0_frame_count = 14;
const uint8_t screen0_w = 12; // px
const uint8_t screen0_h = 19; // px
const uint8_t screen0_period = 25; // ms
